Tinkerforge/hat-brick/software/src/communication.c

/* hat-brick
 * Copyright (C) 2019, 2021 Olaf Lüke <olaf@tinkerforge.com>
 *
 * communication.c: TFP protocol message handling
 *
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
 * You should have received a copy of the GNU Lesser General Public
 * License along with this library; if not, write to the
 * Free Software Foundation, Inc., 59 Temple Place - Suite 330,
 * Boston, MA 02111-1307, USA.
 */

#include "communication.h"

#include "bricklib2/utility/communication_callback.h"
#include "bricklib2/utility/util_definitions.h"
#include "bricklib2/hal/system_timer/system_timer.h"
#include "bricklib2/protocols/tfp/tfp.h"

#include "configs/config_rpi.h"
#include "rpi.h"
#include "voltage.h"
#include "eeprom.h"
#include "xmc_gpio.h"

BootloaderHandleMessageResponse handle_message(const void *message, void *response) {
	switch(tfp_get_fid_from_message(message)) {
		case FID_SET_SLEEP_MODE: return set_sleep_mode(message);
		case FID_GET_SLEEP_MODE: return get_sleep_mode(message, response);
		case FID_SET_BRICKLET_POWER: return set_bricklet_power(message);
		case FID_GET_BRICKLET_POWER: return get_bricklet_power(message, response);
		case FID_GET_VOLTAGES: return get_voltages(message, response);
		case FID_SET_VOLTAGES_CALLBACK_CONFIGURATION: return set_voltages_callback_configuration(message);
		case FID_GET_VOLTAGES_CALLBACK_CONFIGURATION: return get_voltages_callback_configuration(message, response);
		case FID_SET_RTC_DRIVER: return set_rtc_driver(message);
		case FID_GET_RTC_DRIVER: return get_rtc_driver(message, response);
		default: return HANDLE_MESSAGE_RESPONSE_NOT_SUPPORTED;
	}
}


BootloaderHandleMessageResponse set_sleep_mode(const SetSleepMode *data) {
	rpi.power_off_delay_start  = system_timer_get_ms();
	rpi.power_off_delay        = data->power_off_delay*1000;
	rpi.power_off_duration     = data->power_off_duration*1000;
	rpi.raspberry_pi_off       = data->raspberry_pi_off;
	rpi.bricklets_off          = data->bricklets_off;
	rpi.enable_sleep_indicator = data->enable_sleep_indicator;

	return HANDLE_MESSAGE_RESPONSE_EMPTY;
}

BootloaderHandleMessageResponse get_sleep_mode(const GetSleepMode *data, GetSleepMode_Response *response) {
	response->header.length          = sizeof(GetSleepMode_Response);
	response->raspberry_pi_off       = rpi.raspberry_pi_off;
	response->bricklets_off          = rpi.bricklets_off;
	response->enable_sleep_indicator = rpi.enable_sleep_indicator;

	if(rpi.power_off_delay_start == 0) {
		response->power_off_delay = 0;
		if(rpi.power_off_duration_start == 0) {
			response->power_off_duration = 0;
		} else {
			response->power_off_duration = MAX(rpi.power_off_duration - (system_timer_get_ms() - rpi.power_off_duration_start), 0)/1000;
		}
	} else {
		response->power_off_duration = rpi.power_off_duration/1000;
		response->power_off_delay    = MAX(rpi.power_off_delay - (system_timer_get_ms() - rpi.power_off_delay_start), 0)/1000;
	}

	return HANDLE_MESSAGE_RESPONSE_NEW_MESSAGE;
}

BootloaderHandleMessageResponse set_bricklet_power(const SetBrickletPower *data) {
	rpi.bricklet_power = data->bricklet_power;

	if(rpi.bricklet_power) {
		XMC_GPIO_SetOutputHigh(RPI_BRICKLET_EN_PIN);
	} else {
		XMC_GPIO_SetOutputLow(RPI_BRICKLET_EN_PIN);
	}

	return HANDLE_MESSAGE_RESPONSE_EMPTY;
}

BootloaderHandleMessageResponse get_bricklet_power(const GetBrickletPower *data, GetBrickletPower_Response *response) {
	response->header.length  = sizeof(GetBrickletPower_Response);
	response->bricklet_power = rpi.bricklet_power;

	return HANDLE_MESSAGE_RESPONSE_NEW_MESSAGE;
}

BootloaderHandleMessageResponse get_voltages(const GetVoltages *data, GetVoltages_Response *response) {
	response->header.length = sizeof(GetVoltages_Response);
	response->voltage_dc    = voltage.voltage_dc;
	response->voltage_usb   = voltage.voltage_usb;

	return HANDLE_MESSAGE_RESPONSE_NEW_MESSAGE;
}

BootloaderHandleMessageResponse set_voltages_callback_configuration(const SetVoltagesCallbackConfiguration *data) {
	voltage.period              = data->period;
	voltage.value_has_to_change = data->value_has_to_change;

	return HANDLE_MESSAGE_RESPONSE_EMPTY;
}

BootloaderHandleMessageResponse get_voltages_callback_configuration(const GetVoltagesCallbackConfiguration *data, GetVoltagesCallbackConfiguration_Response *response) {
	response->header.length       = sizeof(GetVoltagesCallbackConfiguration_Response);
	response->period              = voltage.period;
	response->value_has_to_change = voltage.value_has_to_change;

	return HANDLE_MESSAGE_RESPONSE_NEW_MESSAGE;
}

BootloaderHandleMessageResponse set_rtc_driver(const SetRTCDriver *data) {
	if(data->rtc_driver > HAT_RTC_DRIVER_DS1338) {
		return HANDLE_MESSAGE_RESPONSE_INVALID_PARAMETER;
	}

	eeprom.rtc_driver = data->rtc_driver;
	eeprom_settings_write();

	return HANDLE_MESSAGE_RESPONSE_EMPTY;
}

BootloaderHandleMessageResponse get_rtc_driver(const GetRTCDriver *data, GetRTCDriver_Response *response) {
	response->header.length = sizeof(GetRTCDriver_Response);
	response->rtc_driver    = eeprom.rtc_driver;

	return HANDLE_MESSAGE_RESPONSE_NEW_MESSAGE;
}

bool handle_voltages_callback(void) {
	static bool is_buffered = false;
	static Voltages_Callback cb;

	static uint32_t last_time = 0;
	static uint16_t last_voltage_usb = 0;
	static uint16_t last_voltage_dc  = 0;

	if(!is_buffered) {
		if(voltage.period == 0 || !system_timer_is_time_elapsed_ms(last_time, voltage.period)) {
			return false;
		}

		if(voltage.value_has_to_change && last_voltage_dc == voltage.voltage_dc && last_voltage_usb == voltage.voltage_usb) {
			return false;
		}

		tfp_make_default_header(&cb.header, bootloader_get_uid(), sizeof(Voltages_Callback), FID_CALLBACK_VOLTAGES);
		cb.voltage_dc    = voltage.voltage_dc;
		cb.voltage_usb   = voltage.voltage_usb;

		last_voltage_dc  = cb.voltage_dc;
		last_voltage_usb = cb.voltage_usb;

		last_time = system_timer_get_ms();
	}

	if(bootloader_spitfp_is_send_possible(&bootloader_status.st)) {
		bootloader_spitfp_send_ack_and_message(&bootloader_status, (uint8_t*)&cb, sizeof(Voltages_Callback));
		is_buffered = false;
		return true;
	} else {
		is_buffered = true;
	}

	return false;
}

void communication_tick(void) {
	communication_callback_tick();
}

void communication_init(void) {
	communication_callback_init();
}
