Tinkerforge/hat-brick/software/src/communication.h

/* hat-bricklet
 * Copyright (C) 2019, 2021 Olaf Lüke <olaf@tinkerforge.com>
 *
 * communication.h: TFP protocol message handling
 *
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
 * You should have received a copy of the GNU Lesser General Public
 * License along with this library; if not, write to the
 * Free Software Foundation, Inc., 59 Temple Place - Suite 330,
 * Boston, MA 02111-1307, USA.
 */

#ifndef COMMUNICATION_H
#define COMMUNICATION_H

#include <stdint.h>
#include <stdbool.h>

#include "bricklib2/protocols/tfp/tfp.h"
#include "bricklib2/bootloader/bootloader.h"

// Default functions
BootloaderHandleMessageResponse handle_message(const void *data, void *response);
void communication_tick(void);
void communication_init(void);

// Constants

#define HAT_RTC_DRIVER_PCF8523 0
#define HAT_RTC_DRIVER_DS1338 1

#define HAT_BOOTLOADER_MODE_BOOTLOADER 0
#define HAT_BOOTLOADER_MODE_FIRMWARE 1
#define HAT_BOOTLOADER_MODE_BOOTLOADER_WAIT_FOR_REBOOT 2
#define HAT_BOOTLOADER_MODE_FIRMWARE_WAIT_FOR_REBOOT 3
#define HAT_BOOTLOADER_MODE_FIRMWARE_WAIT_FOR_ERASE_AND_REBOOT 4

#define HAT_BOOTLOADER_STATUS_OK 0
#define HAT_BOOTLOADER_STATUS_INVALID_MODE 1
#define HAT_BOOTLOADER_STATUS_NO_CHANGE 2
#define HAT_BOOTLOADER_STATUS_ENTRY_FUNCTION_NOT_PRESENT 3
#define HAT_BOOTLOADER_STATUS_DEVICE_IDENTIFIER_INCORRECT 4
#define HAT_BOOTLOADER_STATUS_CRC_MISMATCH 5

#define HAT_STATUS_LED_CONFIG_OFF 0
#define HAT_STATUS_LED_CONFIG_ON 1
#define HAT_STATUS_LED_CONFIG_SHOW_HEARTBEAT 2
#define HAT_STATUS_LED_CONFIG_SHOW_STATUS 3

// Function and callback IDs and structs
#define FID_SET_SLEEP_MODE 1
#define FID_GET_SLEEP_MODE 2
#define FID_SET_BRICKLET_POWER 3
#define FID_GET_BRICKLET_POWER 4
#define FID_GET_VOLTAGES 5
#define FID_SET_VOLTAGES_CALLBACK_CONFIGURATION 6
#define FID_GET_VOLTAGES_CALLBACK_CONFIGURATION 7
#define FID_SET_RTC_DRIVER 9
#define FID_GET_RTC_DRIVER 10

#define FID_CALLBACK_VOLTAGES 8

typedef struct {
	TFPMessageHeader header;
	uint32_t power_off_delay;
	uint32_t power_off_duration;
	bool raspberry_pi_off;
	bool bricklets_off;
	bool enable_sleep_indicator;
} __attribute__((__packed__)) SetSleepMode;

typedef struct {
	TFPMessageHeader header;
} __attribute__((__packed__)) GetSleepMode;

typedef struct {
	TFPMessageHeader header;
	uint32_t power_off_delay;
	uint32_t power_off_duration;
	bool raspberry_pi_off;
	bool bricklets_off;
	bool enable_sleep_indicator;
} __attribute__((__packed__)) GetSleepMode_Response;

typedef struct {
	TFPMessageHeader header;
	bool bricklet_power;
} __attribute__((__packed__)) SetBrickletPower;

typedef struct {
	TFPMessageHeader header;
} __attribute__((__packed__)) GetBrickletPower;

typedef struct {
	TFPMessageHeader header;
	bool bricklet_power;
} __attribute__((__packed__)) GetBrickletPower_Response;

typedef struct {
	TFPMessageHeader header;
} __attribute__((__packed__)) GetVoltages;

typedef struct {
	TFPMessageHeader header;
	uint16_t voltage_usb;
	uint16_t voltage_dc;
} __attribute__((__packed__)) GetVoltages_Response;

typedef struct {
	TFPMessageHeader header;
	uint32_t period;
	bool value_has_to_change;
} __attribute__((__packed__)) SetVoltagesCallbackConfiguration;

typedef struct {
	TFPMessageHeader header;
} __attribute__((__packed__)) GetVoltagesCallbackConfiguration;

typedef struct {
	TFPMessageHeader header;
	uint32_t period;
	bool value_has_to_change;
} __attribute__((__packed__)) GetVoltagesCallbackConfiguration_Response;

typedef struct {
	TFPMessageHeader header;
	uint16_t voltage_usb;
	uint16_t voltage_dc;
} __attribute__((__packed__)) Voltages_Callback;

typedef struct {
	TFPMessageHeader header;
	uint8_t rtc_driver;
} __attribute__((__packed__)) SetRTCDriver;

typedef struct {
	TFPMessageHeader header;
} __attribute__((__packed__)) GetRTCDriver;

typedef struct {
	TFPMessageHeader header;
	uint8_t rtc_driver;
} __attribute__((__packed__)) GetRTCDriver_Response;


// Function prototypes
BootloaderHandleMessageResponse set_sleep_mode(const SetSleepMode *data);
BootloaderHandleMessageResponse get_sleep_mode(const GetSleepMode *data, GetSleepMode_Response *response);
BootloaderHandleMessageResponse set_bricklet_power(const SetBrickletPower *data);
BootloaderHandleMessageResponse get_bricklet_power(const GetBrickletPower *data, GetBrickletPower_Response *response);
BootloaderHandleMessageResponse get_voltages(const GetVoltages *data, GetVoltages_Response *response);
BootloaderHandleMessageResponse set_voltages_callback_configuration(const SetVoltagesCallbackConfiguration *data);
BootloaderHandleMessageResponse get_voltages_callback_configuration(const GetVoltagesCallbackConfiguration *data, GetVoltagesCallbackConfiguration_Response *response);
BootloaderHandleMessageResponse set_rtc_driver(const SetRTCDriver *data);
BootloaderHandleMessageResponse get_rtc_driver(const GetRTCDriver *data, GetRTCDriver_Response *response);

// Callbacks
bool handle_voltages_callback(void);

#define COMMUNICATION_CALLBACK_TICK_WAIT_MS 1
#define COMMUNICATION_CALLBACK_HANDLER_NUM 1
#define COMMUNICATION_CALLBACK_LIST_INIT \
	handle_voltages_callback, \


#endif
